AJ6CU/32bit-Raduino-Board_Designs/RaduinoClone/Nano Family Nano-Every-IOT-BLE-RP2040/uBitxV6Specific/Images/uBitx V6 Raduino Clone Rev 6.A Arduino Nano Family-front.jpg

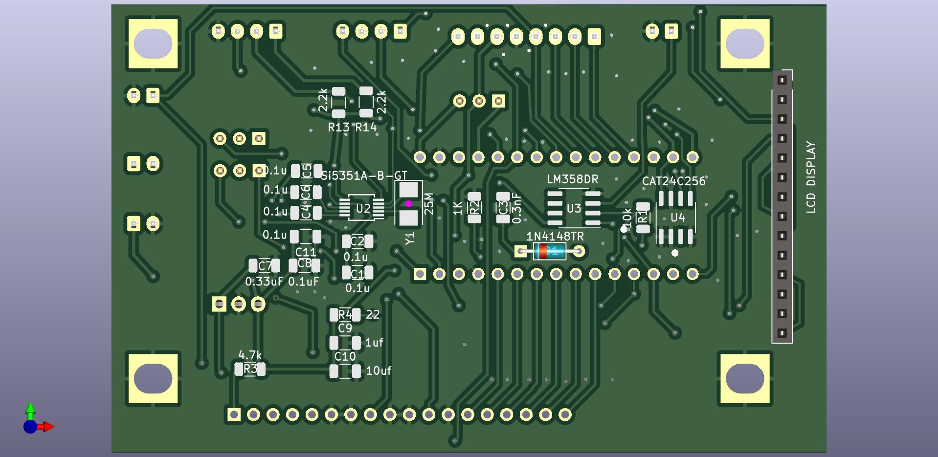
RaduinoClone/Nano Family Nano-Every-IOT-BLE-RP2040/uBitxV6Specific/Images/uBitx V6 Raduino Clone Rev 6.A Arduino Nano Family-front.jpg
