AJ6CU/32bit-Raduino-Board_Designs/RaduinoClone/Nano Family Nano-Every-IOT-BLE-RP2040/uBitxV3456/Images/uBitx V3-6 Raduino Clone Rev 6.A Arduino Nano Family-rear.jpg

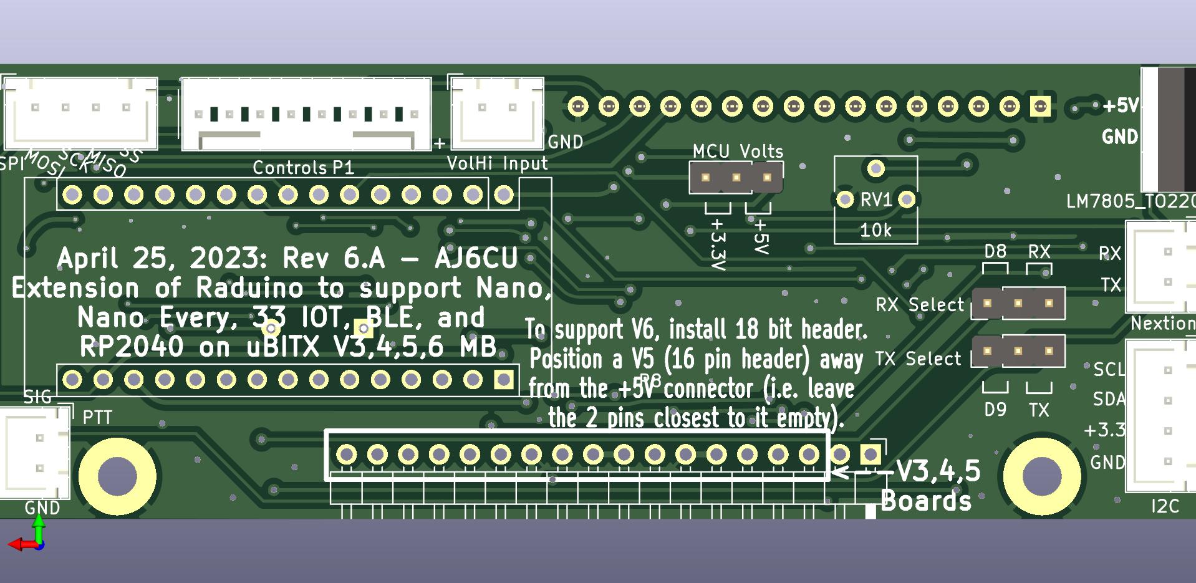
RaduinoClone/Nano Family Nano-Every-IOT-BLE-RP2040/uBitxV3456/Images/uBitx V3-6 Raduino Clone Rev 6.A Arduino Nano Family-rear.jpg
