AJ6CU/32bit-Raduino-Board_Designs/RaduinoClone/RaspberryPiPico/uBitxV6Specific/Images/uBitx V6 Raduino Clone Rev 6.A pico-front.jpg

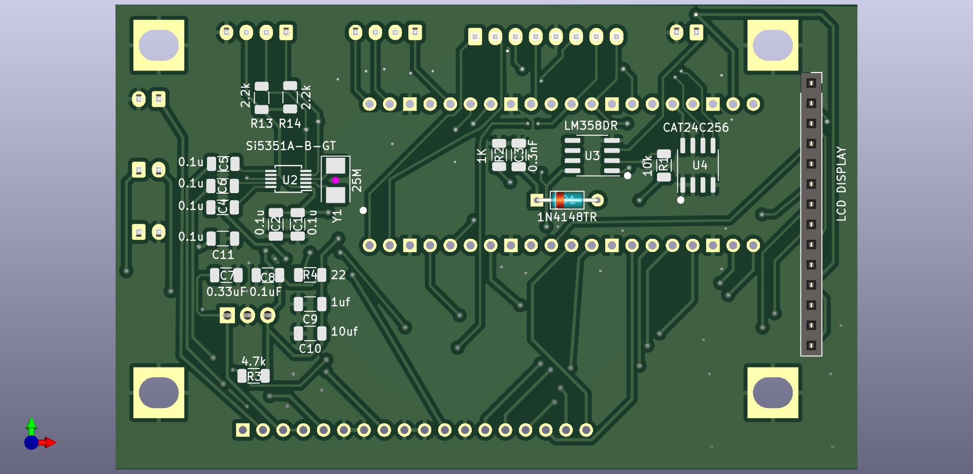
RaduinoClone/RaspberryPiPico/uBitxV6Specific/Images/uBitx V6 Raduino Clone Rev 6.A pico-front.jpg
