AJ6CU/32bit-Raduino-Board_Designs/RaduinoClone/RaspberryPiPico/uBitxV3456/Images/uBitx V3-6 Raduino Clone Rev 6.A pico-rear.jpg

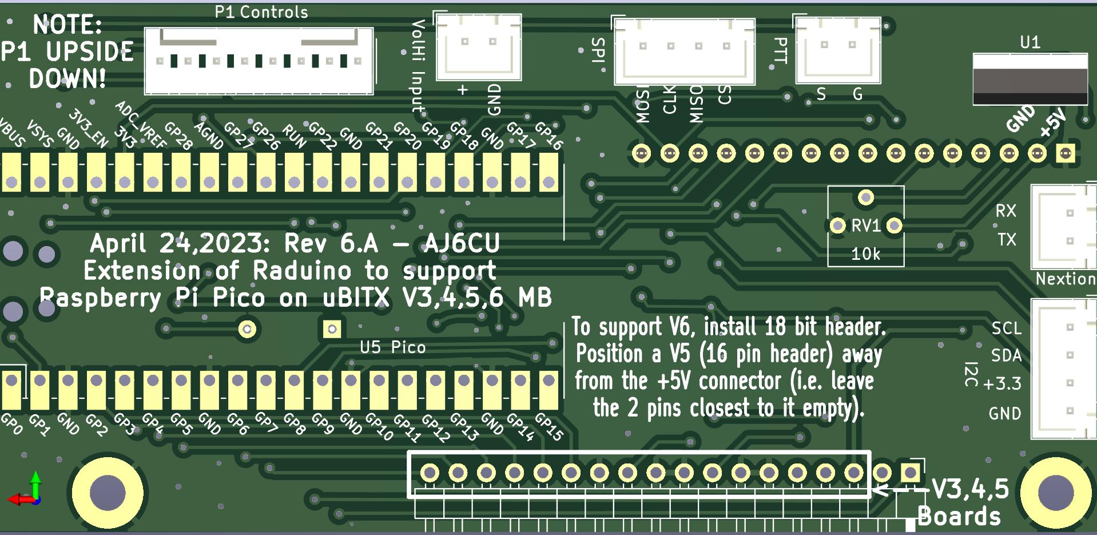
RaduinoClone/RaspberryPiPico/uBitxV3456/Images/uBitx V3-6 Raduino Clone Rev 6.A pico-rear.jpg
