AJ6CU/32bit-Raduino-Board_Designs/RaduinoClone/RaspberryPiZeroW2/uBitxV6Specific/Images/uBitx V6 Raduino Clone Rev 10-Optic piZero2w-FrontView.jpg

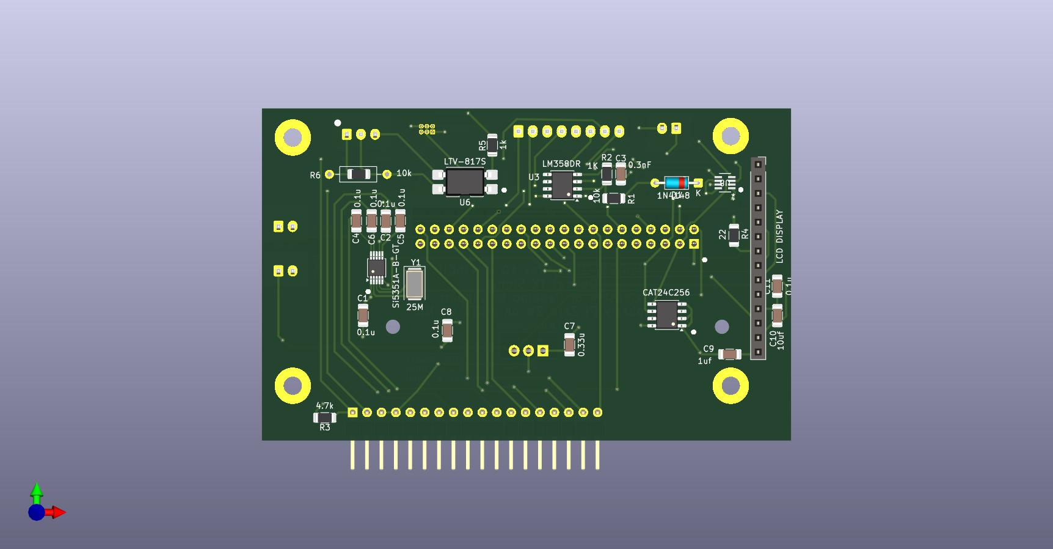
RaduinoClone/RaspberryPiZeroW2/uBitxV6Specific/Images/uBitx V6 Raduino Clone Rev 10-Optic piZero2w-FrontView.jpg
