AJ6CU/32bit-Raduino-Board_Designs/RaduinoClone/Teensy 4.1/uBitxV6Specific/Images/uBitx V6 Raduino Clone Rev 6.A teensy 4.1-front.jpg

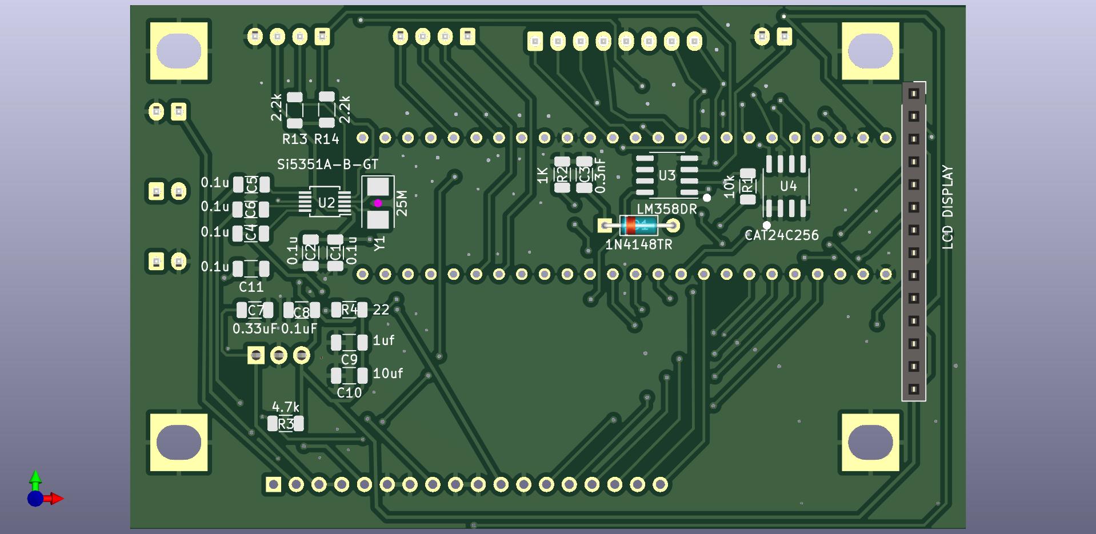
RaduinoClone/Teensy 4.1/uBitxV6Specific/Images/uBitx V6 Raduino Clone Rev 6.A teensy 4.1-front.jpg
