AJ6CU/32bit-Raduino-Board_Designs/RaduinoClone/Teensy 4.1/uBitxV3456/Images/uBitx V3-6 Raduino Clone Rev 6.A teensy 4.1-rear.jpg

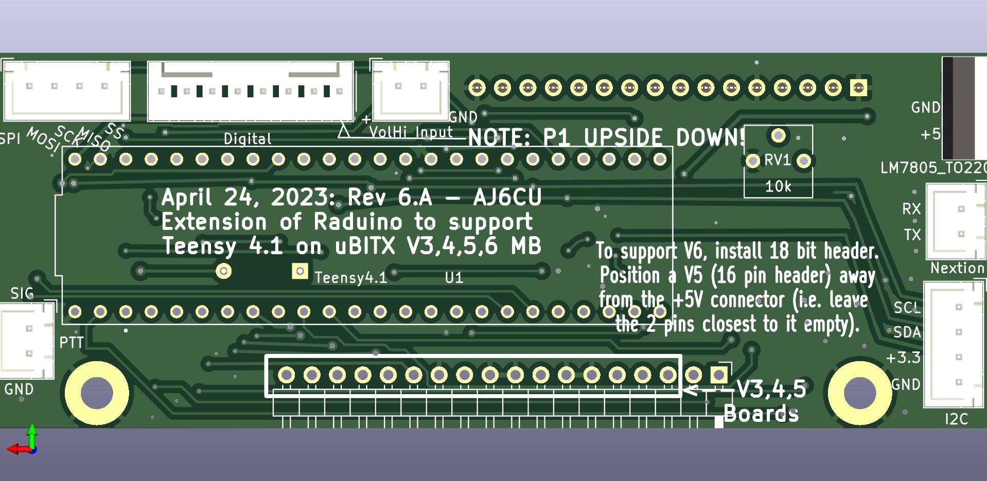
RaduinoClone/Teensy 4.1/uBitxV3456/Images/uBitx V3-6 Raduino Clone Rev 6.A teensy 4.1-rear.jpg
